formix/S80/Software/S80 Ver 1_0/Towers of Hanoi/S80_ansi.c

//===============================================================================
//
// Project: S80_towers_of_hanoi
// File:    S80_ansi.c
// Version: 1.0
//
// Author : Filip Pynckels
//
// Created: 2018 11 05
// Adapted: 2018 11 05
//
//===============================================================================
//
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
//===============================================================================


//===============================================================================
//=   I N C L U D E S                                                           =
//===============================================================================

#include <stdio.h>

#include "S80_ansi.h"
#include "S80_serial.h"


//===============================================================================
//=   C O D E                                                                   =
//===============================================================================

	//---------------------------------------------------------------------------
	//- Screen functions                                                        -
	//---------------------------------------------------------------------------

	void ClearScreen (void)
		{
		SendString(CLEARSCREEN);
		}

	void ResetAttributes (void)
		{
		SendString(RESETATTRIB);
		}

	//---------------------------------------------------------------------------
	//- Cursor functions                                                        -
	//-   Position is 1-based.                                                  -
	//-   Home position is (1,1)                                                -
	//---------------------------------------------------------------------------

	void CursorHome (void)
		{
		SendString(CURSORHOME);
		}

	void CursorXY (unsigned char x, unsigned char y)
		{
		char buffer[30];
		
		sprintf(buffer, CURSORXY, y, x);
		SendString(buffer);
		}

	//---------------------------------------------------------------------------
	//- Color functions                                                         -
	//---------------------------------------------------------------------------

	void SetColor (
		unsigned char fgColor, unsigned char fgBright,
		unsigned char bgColor, unsigned char bgBright
		)
		
		{
		char buffer[50];
		char fgCommand[25];
		char bgCommand[25];

		if (fgBright == NOTBRIGHT)
			sprintf(fgCommand, FGCOLOR, fgColor);
		else
			sprintf(fgCommand, FGBRCOLOR, fgColor);

		if (bgBright == NOTBRIGHT)
			sprintf(bgCommand, BGCOLOR, bgColor);
		else
			sprintf(bgCommand, BGBRCOLOR, bgColor);

		sprintf(buffer, "%s%s", fgCommand, bgCommand);
		SendString(buffer);
		}
	
	void SetColorRGB (
		unsigned char fgR, unsigned char fgG, unsigned char fgB,
		unsigned char bgR, unsigned char bgG, unsigned char bgB
		)

		{
		char buffer[50];
		char fgCommand[25];
		char bgCommand[25];

		sprintf(fgCommand, FGRGBCOLOR, fgR, fgG, fgB);
		sprintf(bgCommand, BGRGBCOLOR, bgR, bgG, bgB);
		sprintf(buffer, "%s%s", fgCommand, bgCommand);
		SendString(buffer);
		}
